MotorDynamicsLab/LDOVoronTrident/STLs/LDOSBCW2MountCover/LDOSBCW2MountCover.3mf

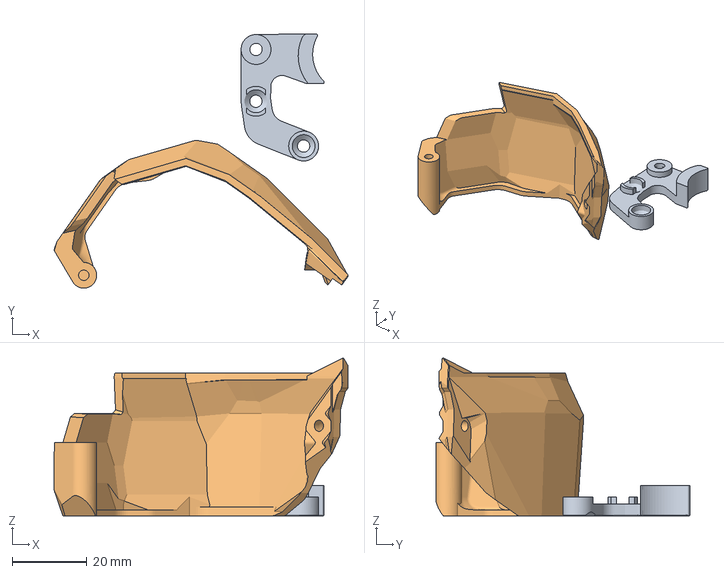
[picture p18: CAD file, 2022-08-31]
STLs/LDOSBCW2MountCover/LDOSBCW2MountCover.3mf
78.6 x 68.0 x 42.2 mm
