MotorDynamicsLab/LDOVoronTrident/STLs/LDOSBCW2MountCover/LDOSBCW2Cover.step

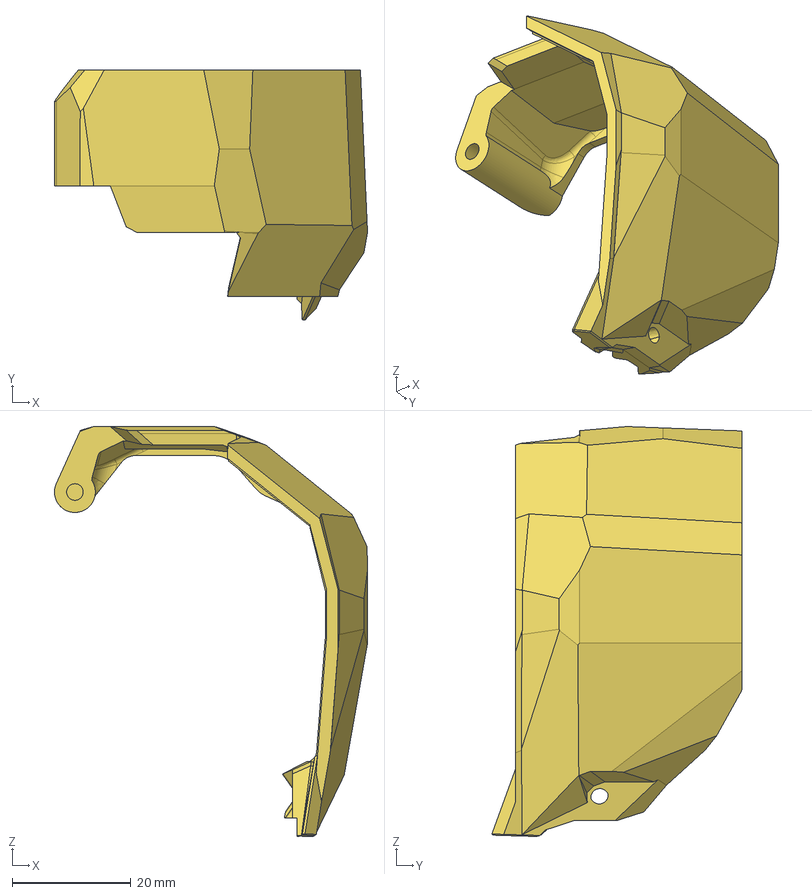
[picture p19: CAD file, 2022-08-31]
STLs/LDOSBCW2MountCover/LDOSBCW2Cover.step
52.8 x 42.2 x 69.1 mm
