MotorDynamicsLab/LDOVoronTrident/STLs/BTT Pi TFT4.3 Mount/mount_thick.stl

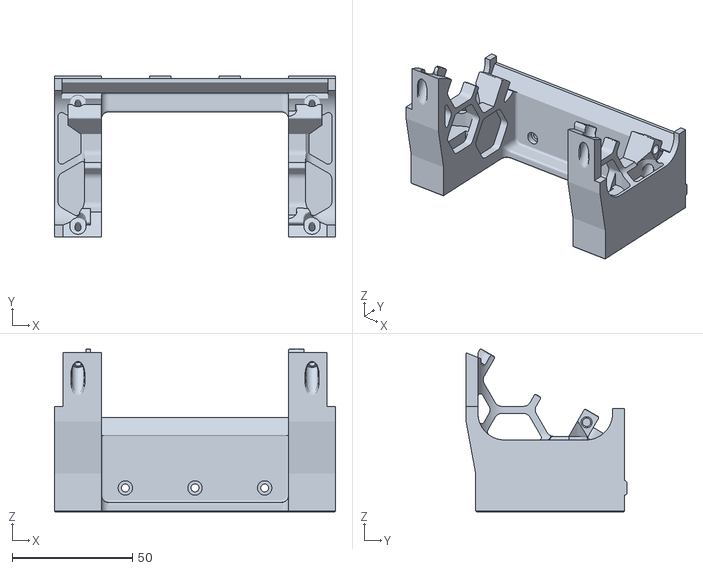
[picture p20: CAD file, 2024-01-23, an earlier design]
STLs/BTT Pi TFT4.3 Mount/mount_thick.stl
117.0 x 67.0 x 67.8
