MotorDynamicsLab/LDOVoronTrident/Images/WiringGuide/250/din_rails_close_up.jpg

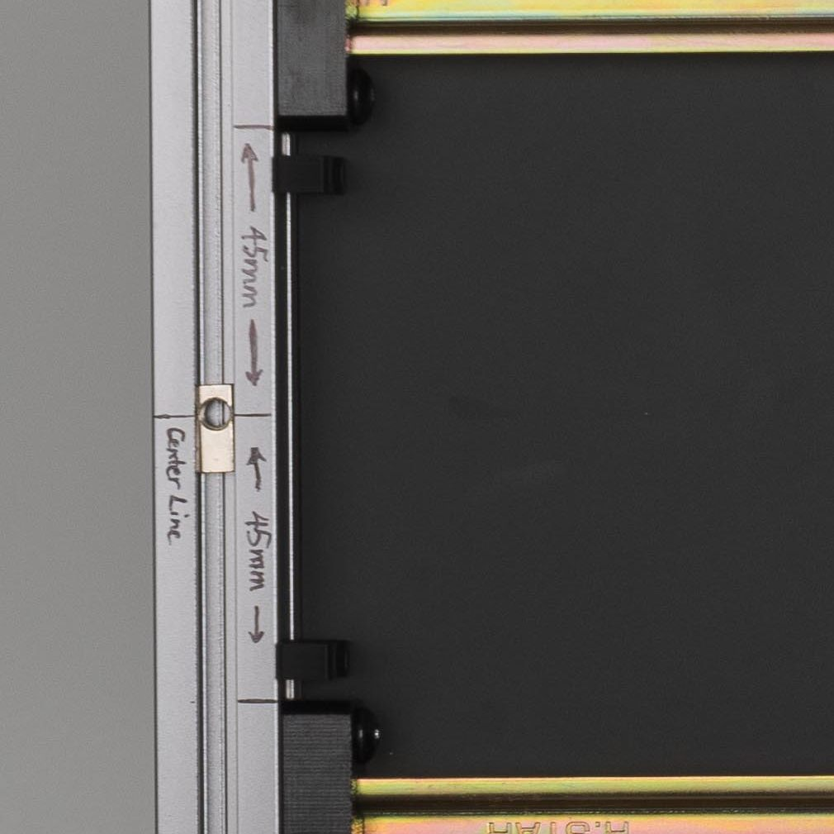
Images/WiringGuide/250/din_rails_close_up.jpg
