MotorDynamicsLab/LDOVoronTrident/Images/WiringGuide/250/fan_pcb_positioning.jpg

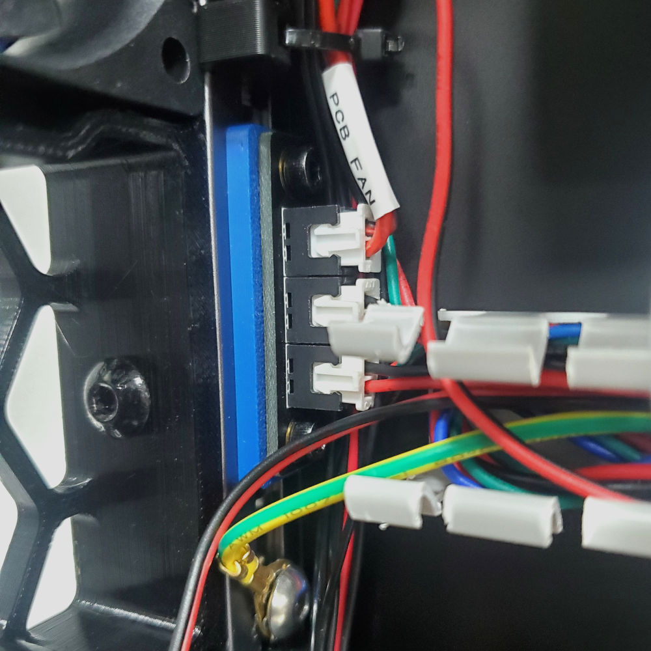
Images/WiringGuide/250/fan_pcb_positioning.jpg
