MotorDynamicsLab/LDOVoronTrident/Images/WiringGuide/250/S01_din_rails.jpg

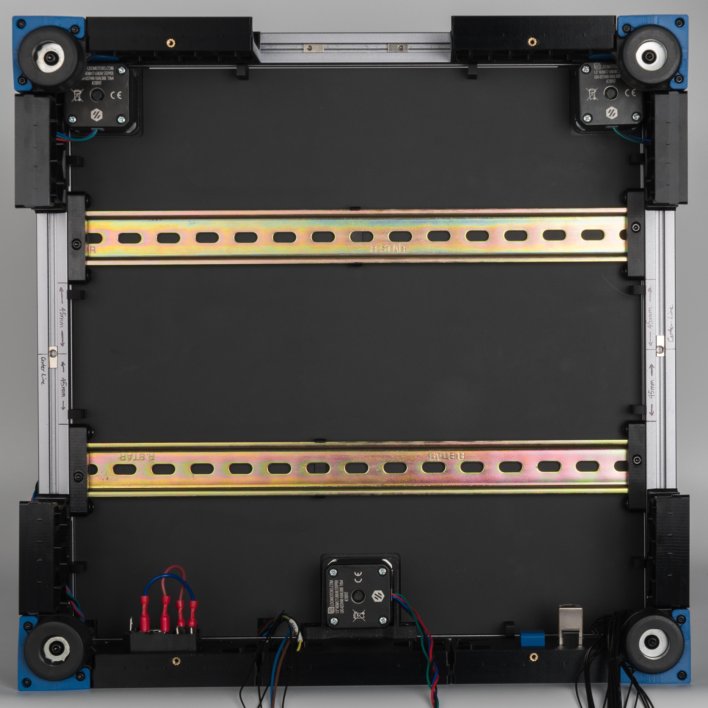
Images/WiringGuide/250/S01_din_rails.jpg
