MotorDynamicsLab/LDOVoronTrident/Images/WiringGuide/250/S02_general_placement.jpg

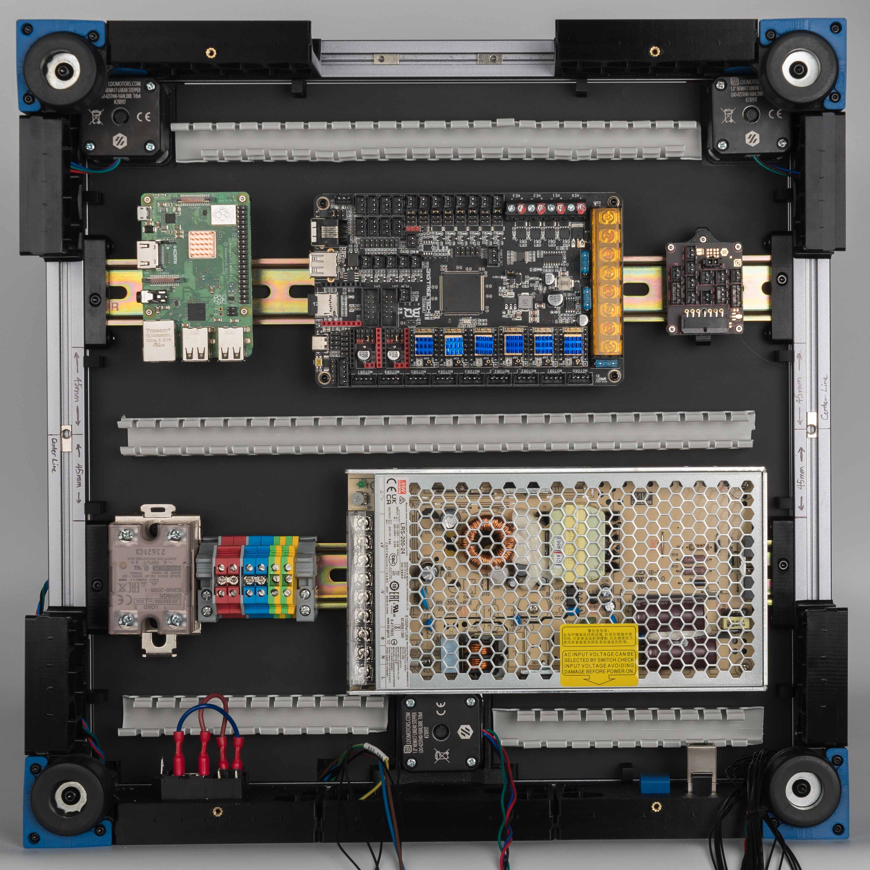
Images/WiringGuide/250/S02_general_placement.jpg
