MotorDynamicsLab/LDOVoronTrident/Images/WiringGuide/250/s03_mapping.png

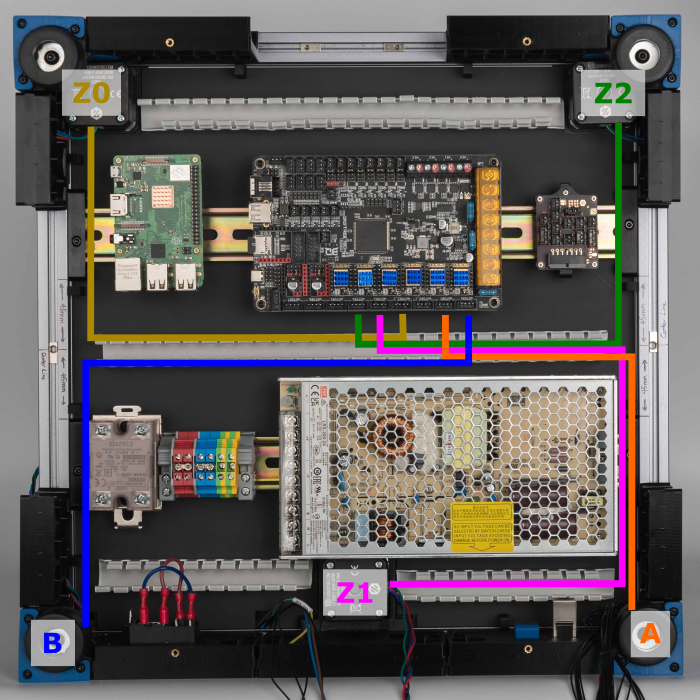
Images/WiringGuide/250/s03_mapping.png
