MotorDynamicsLab/LDOVoronTrident/Images/WiringGuide/250/S03_steppers.jpg

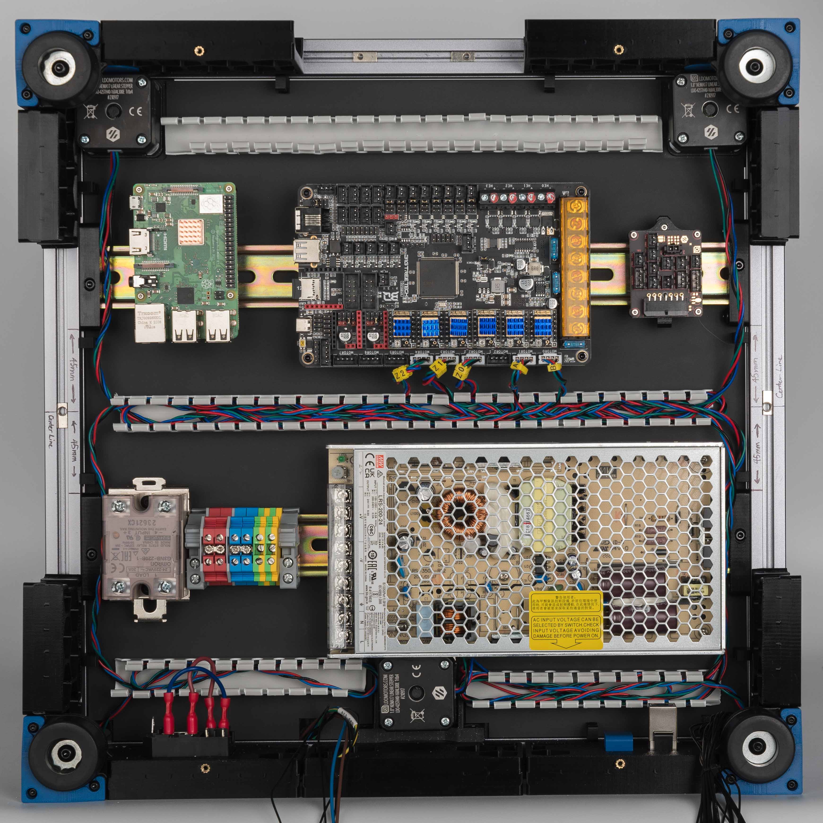
Images/WiringGuide/250/S03_steppers.jpg
