MotorDynamicsLab/LDOVoronTrident/Images/WiringGuide/250/s04_inlet_psu.jpg

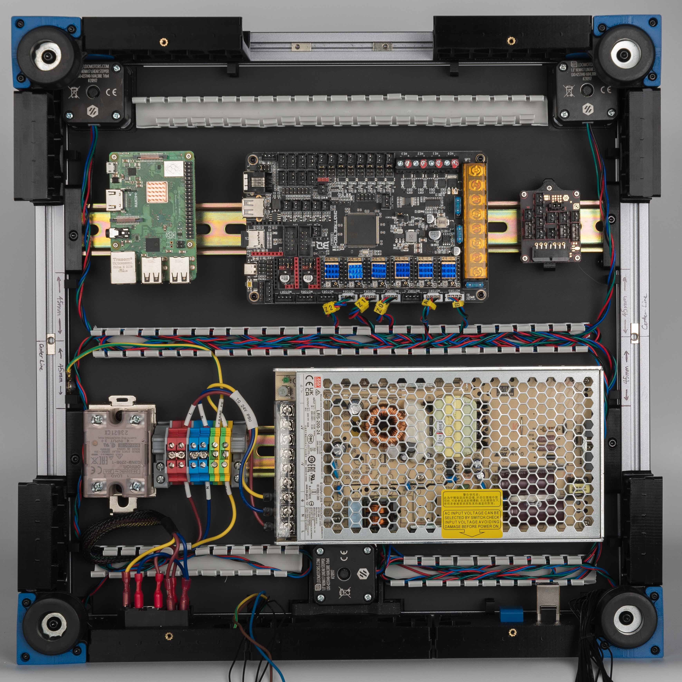
Images/WiringGuide/250/s04_inlet_psu.jpg
