MotorDynamicsLab/LDOVoronTrident/Images/WiringGuide/250/s04_mapping.png

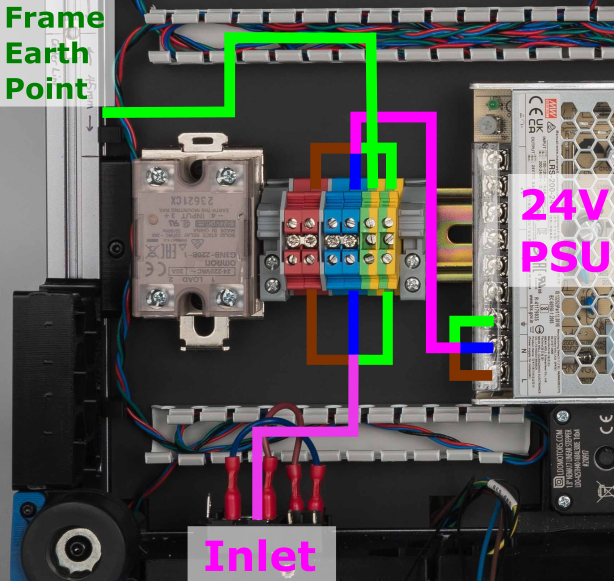
Images/WiringGuide/250/s04_mapping.png
