MotorDynamicsLab/LDOVoronTrident/Images/WiringGuide/250/s06_bed_controller.jpg

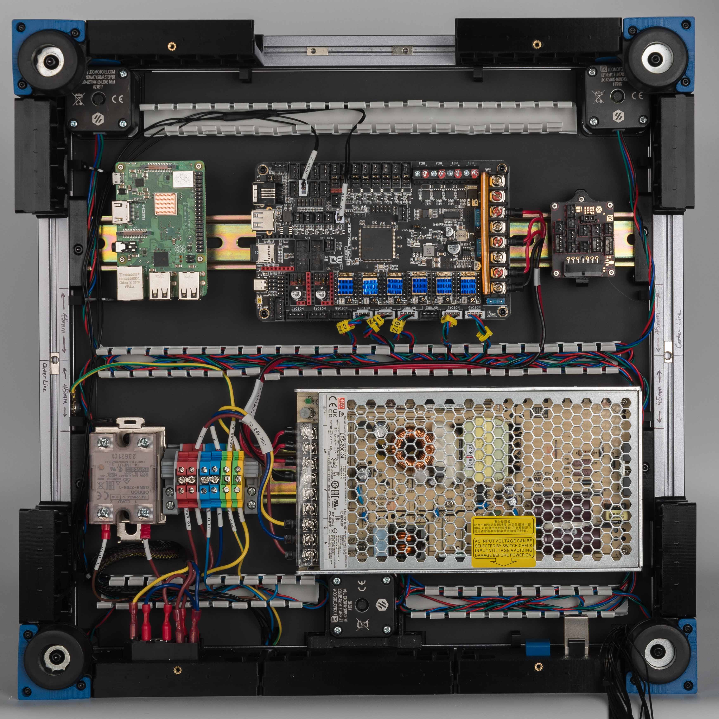
Images/WiringGuide/250/s06_bed_controller.jpg
