MotorDynamicsLab/LDOVoronTrident/Images/WiringGuide/250/s06_mapping.png

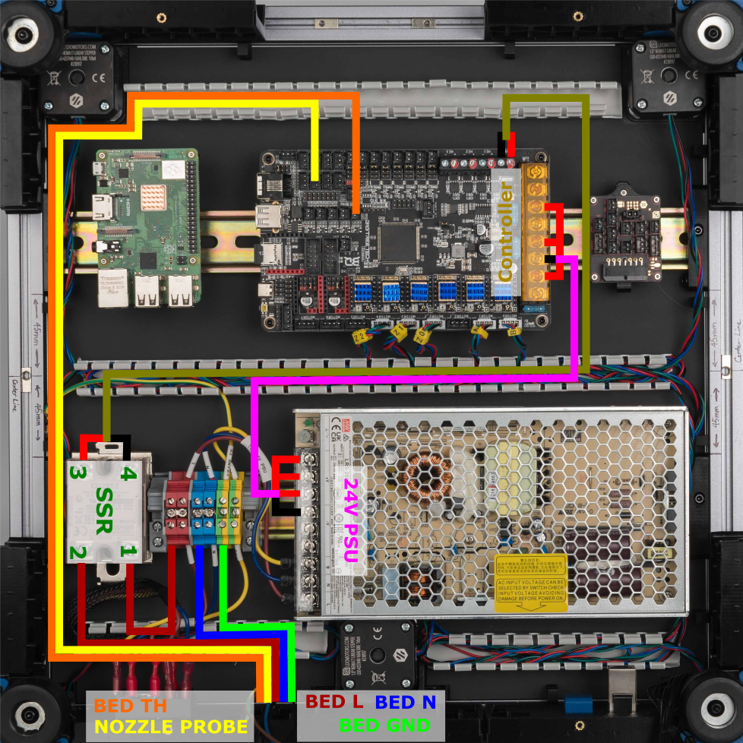
Images/WiringGuide/250/s06_mapping.png
