MotorDynamicsLab/LDOVoronTrident/Images/WiringGuide/250/s07_mapping.png

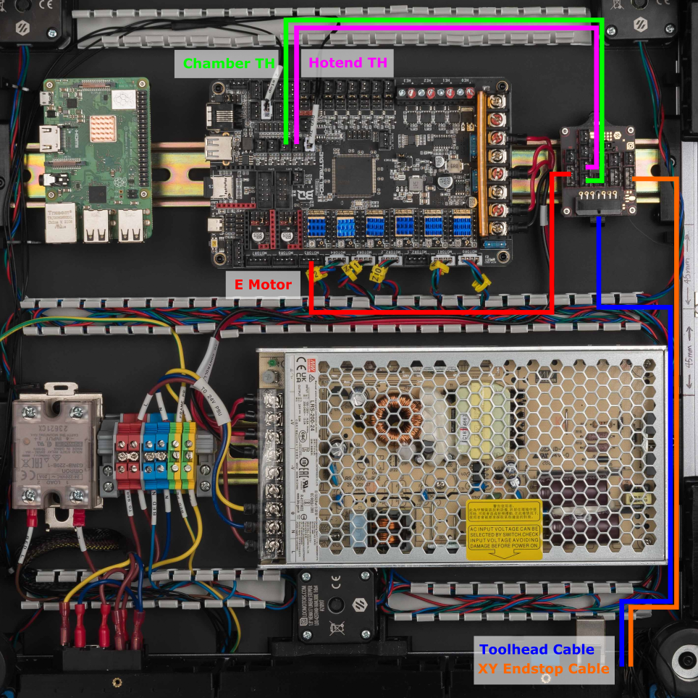
Images/WiringGuide/250/s07_mapping.png
