MotorDynamicsLab/LDOVoronTrident/Images/WiringGuide/250/s07_toolhead_th_motor.jpg

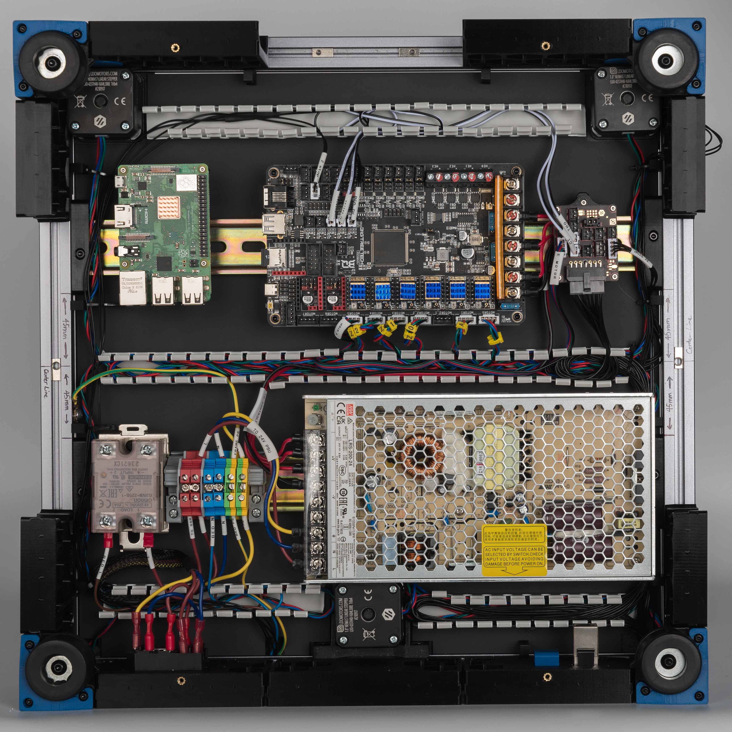
Images/WiringGuide/250/s07_toolhead_th_motor.jpg
