MotorDynamicsLab/LDOVoronTrident/Images/WiringGuide/250/s08_mapping.png

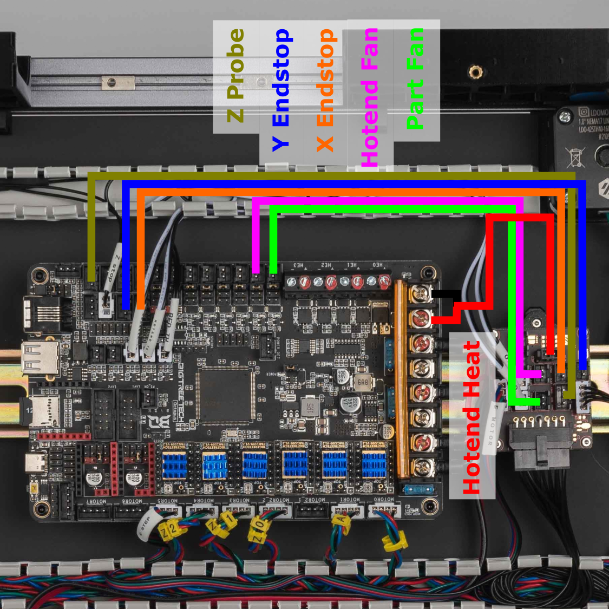
Images/WiringGuide/250/s08_mapping.png
