MotorDynamicsLab/LDOVoronTrident/Images/WiringGuide/250/s09_mapping.png

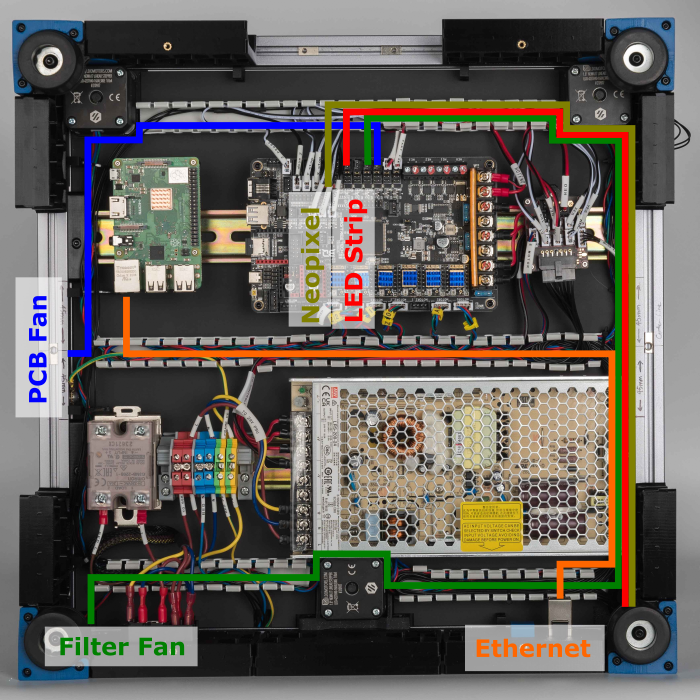
Images/WiringGuide/250/s09_mapping.png
