MotorDynamicsLab/LDOVoronTrident/Images/WiringGuide/250/s09_misc.jpg

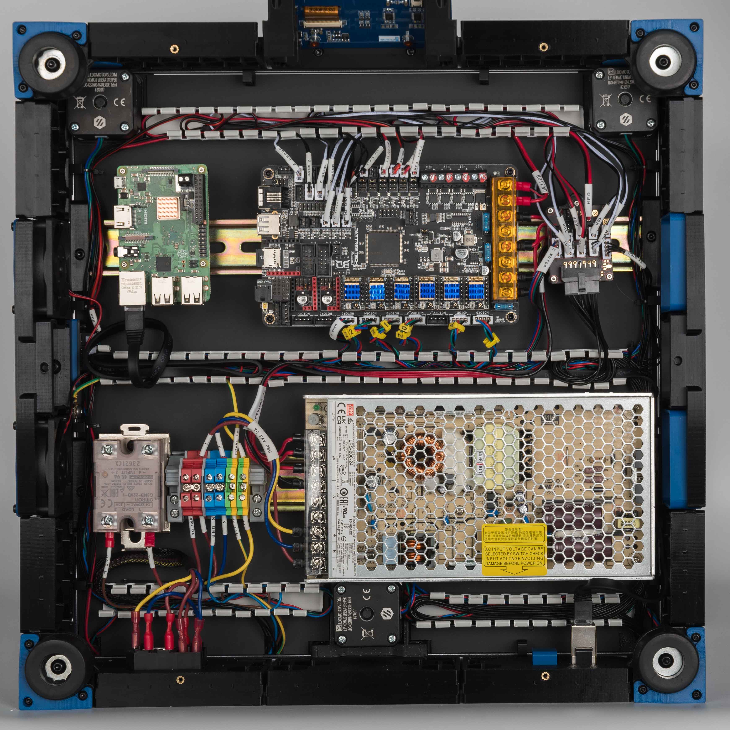
Images/WiringGuide/250/s09_misc.jpg
