MotorDynamicsLab/LDOVoronTrident/Images/WiringGuide/250/s10_mapping.png

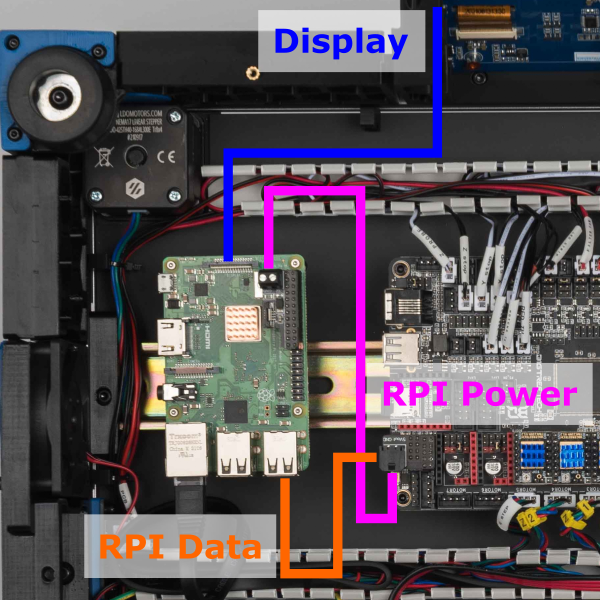
Images/WiringGuide/250/s10_mapping.png
