MotorDynamicsLab/LDOVoronTrident/Images/WiringGuide/250/s10_rpi.jpg

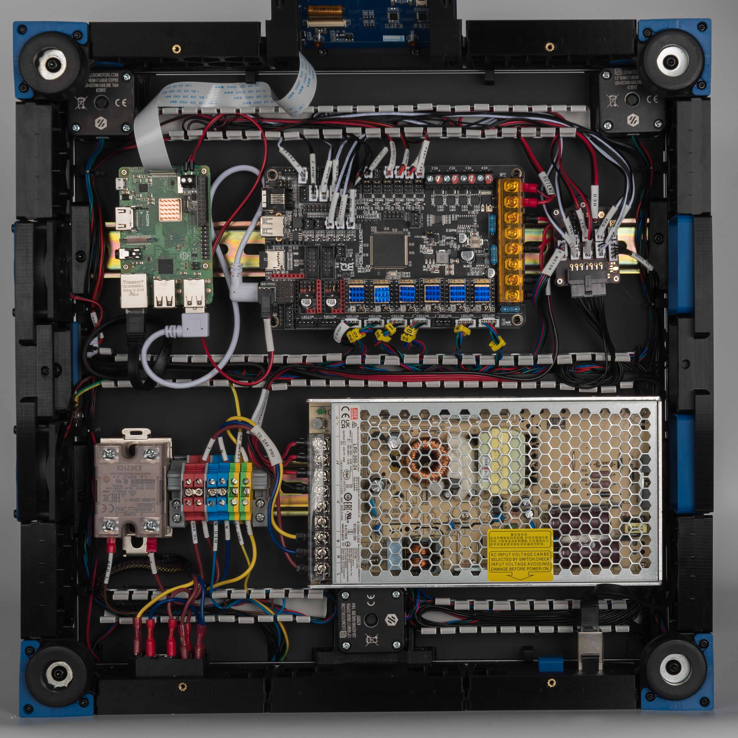
Images/WiringGuide/250/s10_rpi.jpg
