MotorDynamicsLab/LDOVoronTrident/Images/WiringGuide/250/s11_duct_cover.jpg

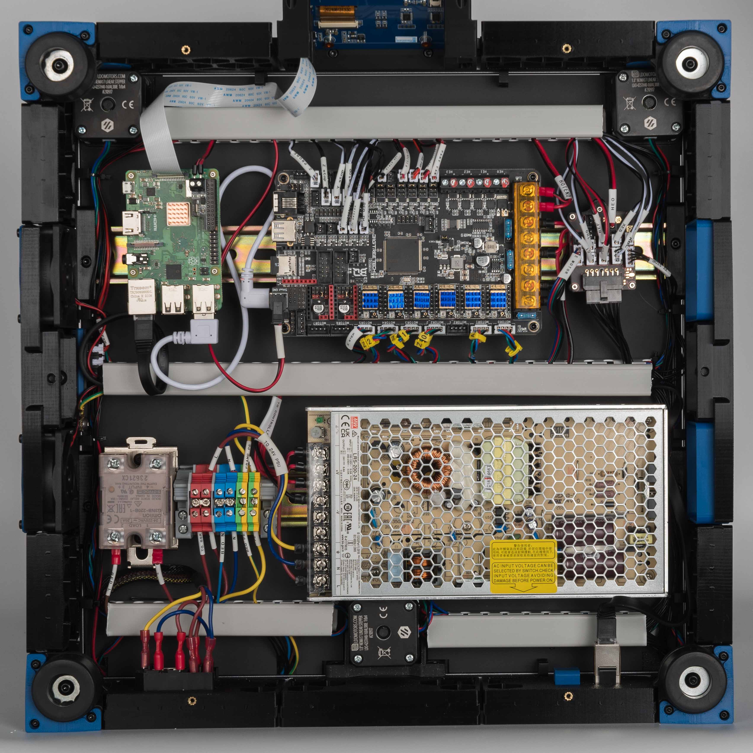
Images/WiringGuide/250/s11_duct_cover.jpg
