MotorDynamicsLab/LDOVoronTrident/Images/WiringGuide/build_plate_unwired.jpg

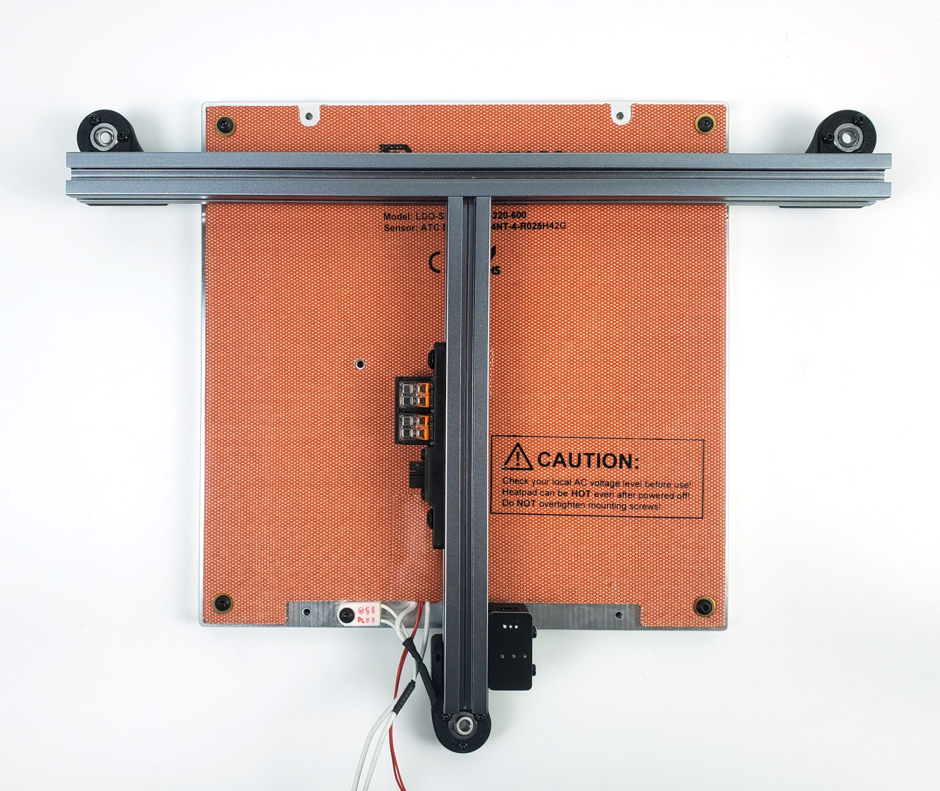
Images/WiringGuide/build_plate_unwired.jpg
