MotorDynamicsLab/LDOVoronTrident/Images/WiringGuide/build_plate_wired.jpg

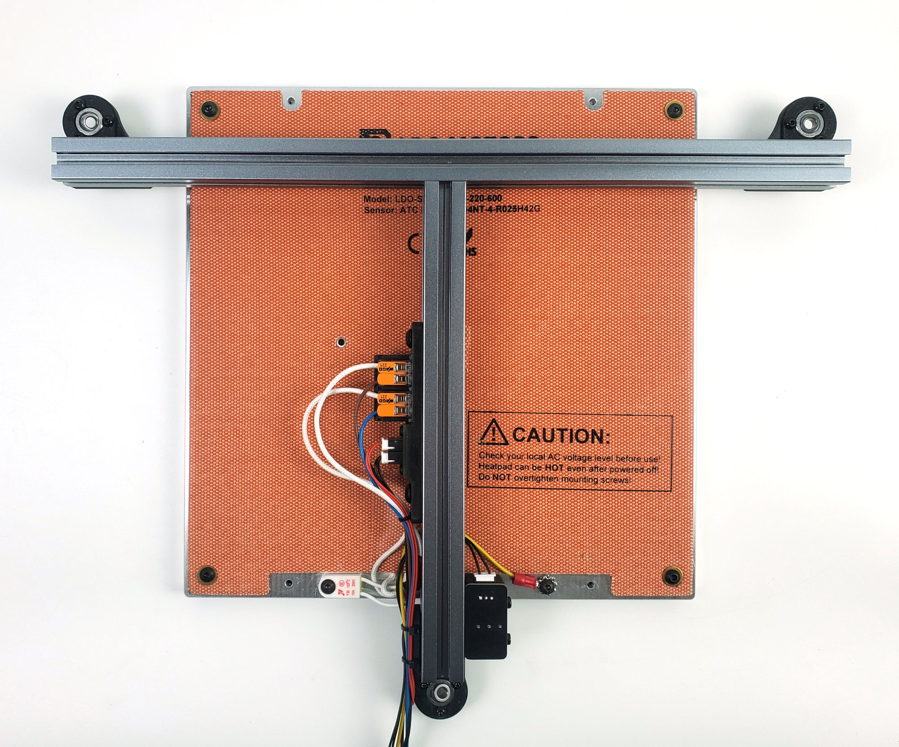
Images/WiringGuide/build_plate_wired.jpg
