MotorDynamicsLab/LDOVoronTrident/Images/WiringGuide/display_connection_a.jpg

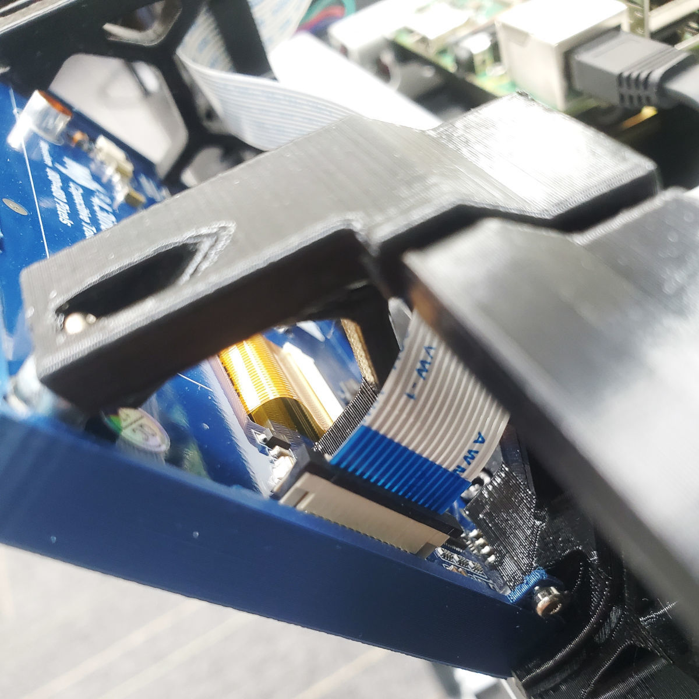
Images/WiringGuide/display_connection_a.jpg
