MotorDynamicsLab/LDOVoronTrident/Images/WiringGuide/display_connection_b.jpg

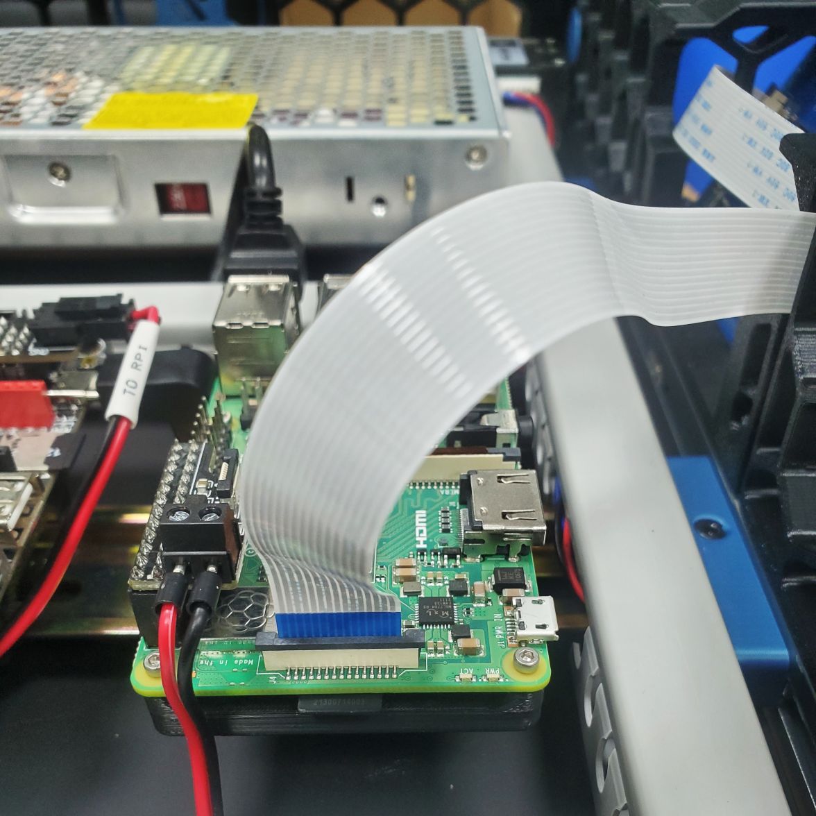
Images/WiringGuide/display_connection_b.jpg
