MotorDynamicsLab/LDOVoronTrident/Images/WiringGuide/frame_grounding.jpg

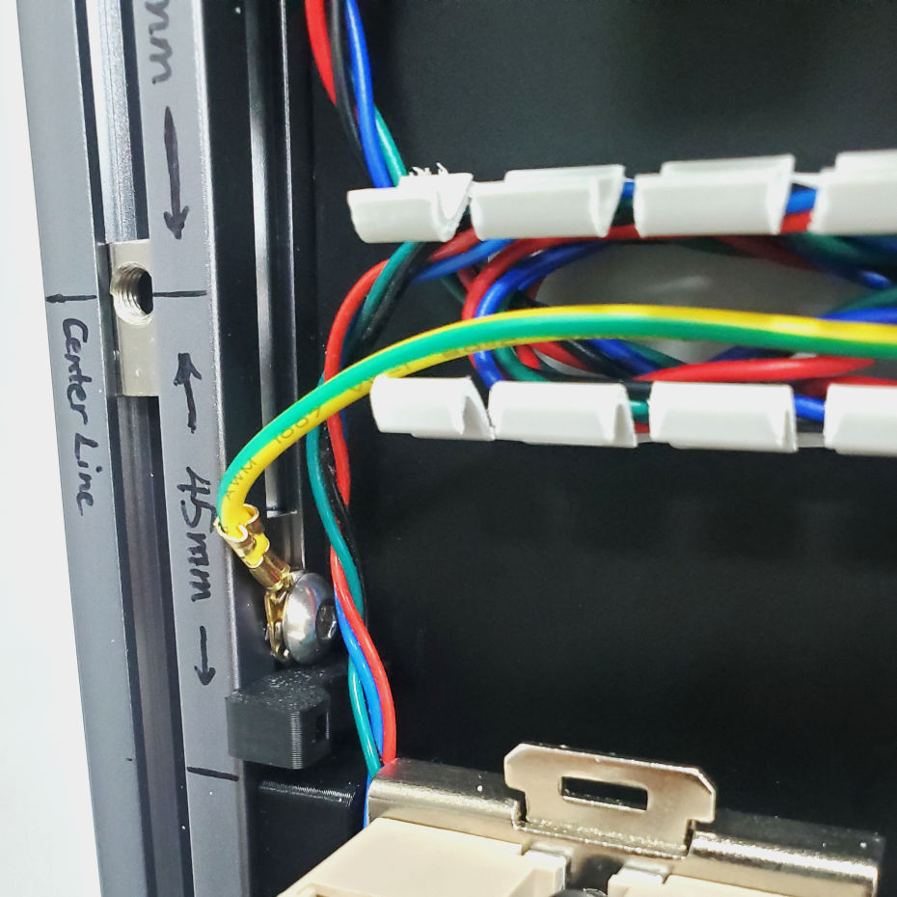
Images/WiringGuide/frame_grounding.jpg
