MotorDynamicsLab/LDOVoronTrident/Images/WiringGuide/led_pcb_positioning.jpg

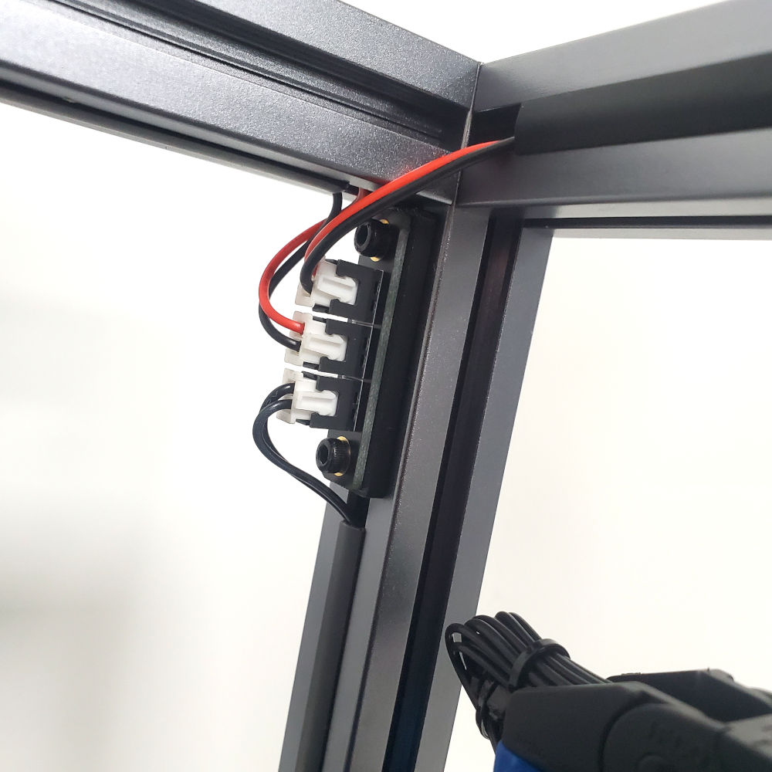
Images/WiringGuide/led_pcb_positioning.jpg
