MotorDynamicsLab/LDOVoronTrident/Images/WiringGuide/led_route.png

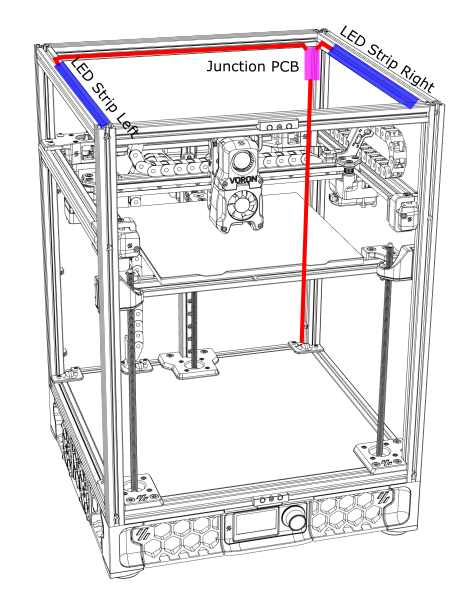
Images/WiringGuide/led_route.png
