MotorDynamicsLab/LDOVoronTrident/Images/WiringGuide/Octopus_Populated.jpg

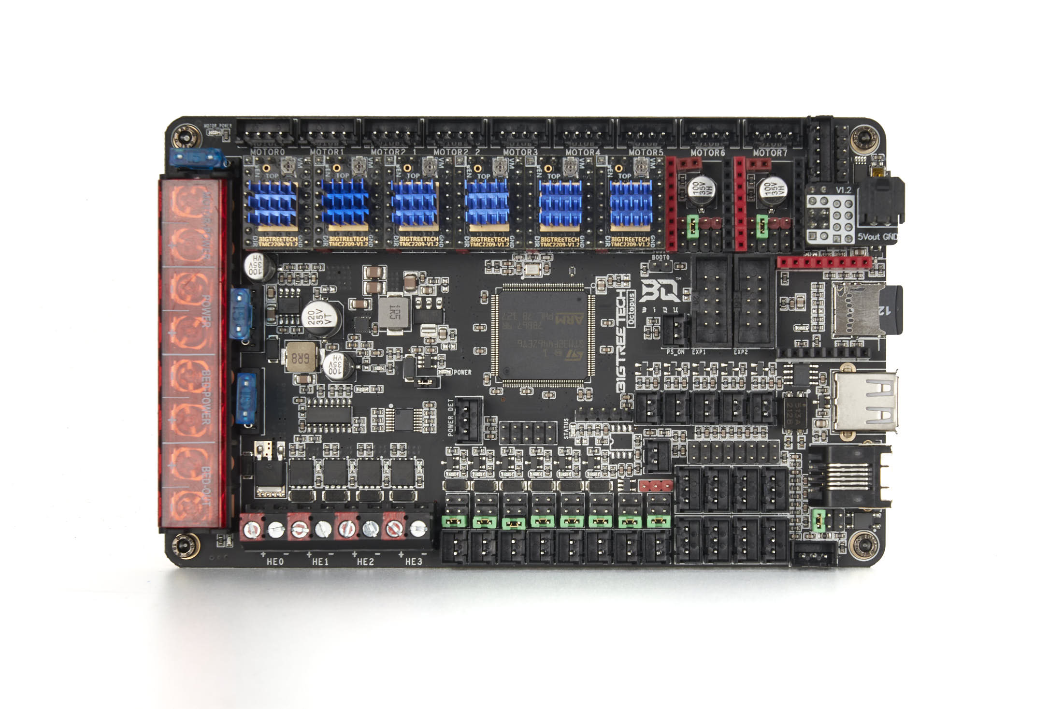
Images/WiringGuide/Octopus_Populated.jpg
