MotorDynamicsLab/LDOVoronTrident/Images/WiringGuide/rail_close_up.png

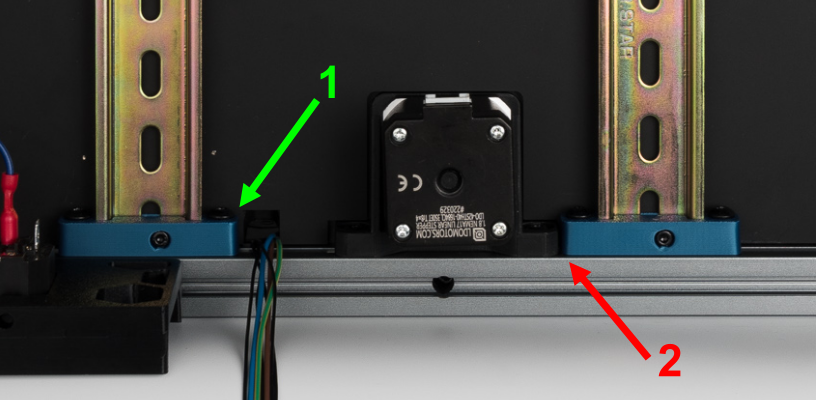
Images/WiringGuide/rail_close_up.png
