MotorDynamicsLab/LDOVoronTrident/Images/WiringGuide/raspi_power_connection.jpg

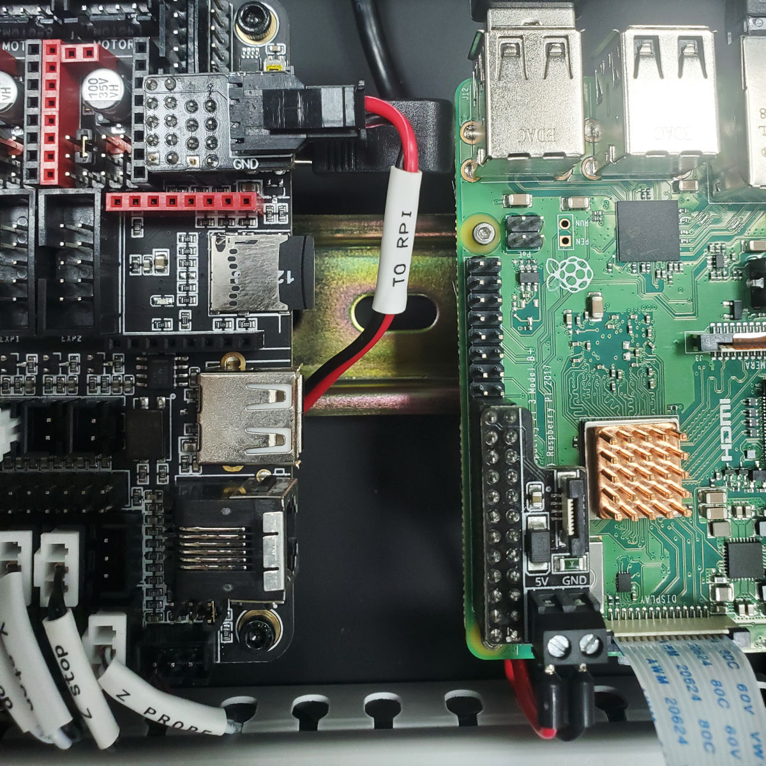
Images/WiringGuide/raspi_power_connection.jpg
