MotorDynamicsLab/LDOVoronTrident/Images/WiringGuide/RevD/00_Din Rail.jpg

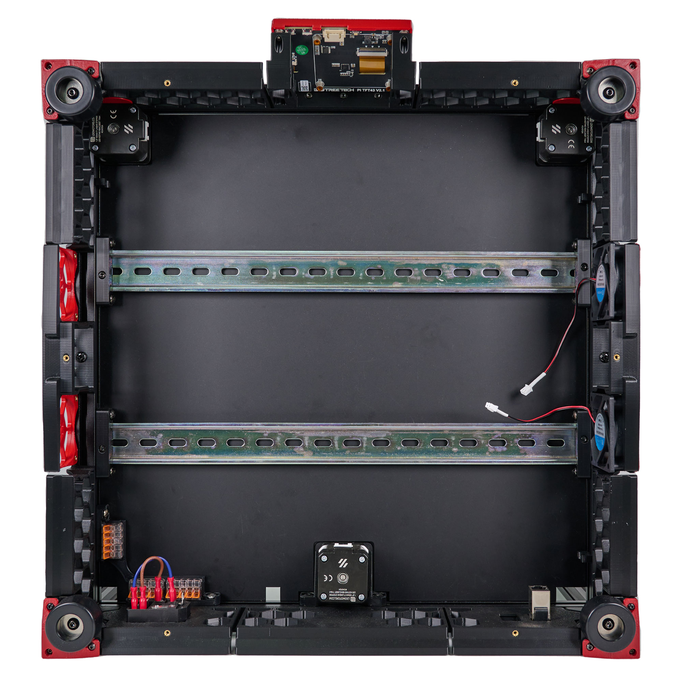
Images/WiringGuide/RevD/00_Din Rail.jpg
