MotorDynamicsLab/LDOVoronTrident/Images/WiringGuide/RevD/00_Gneral Placement.jpg

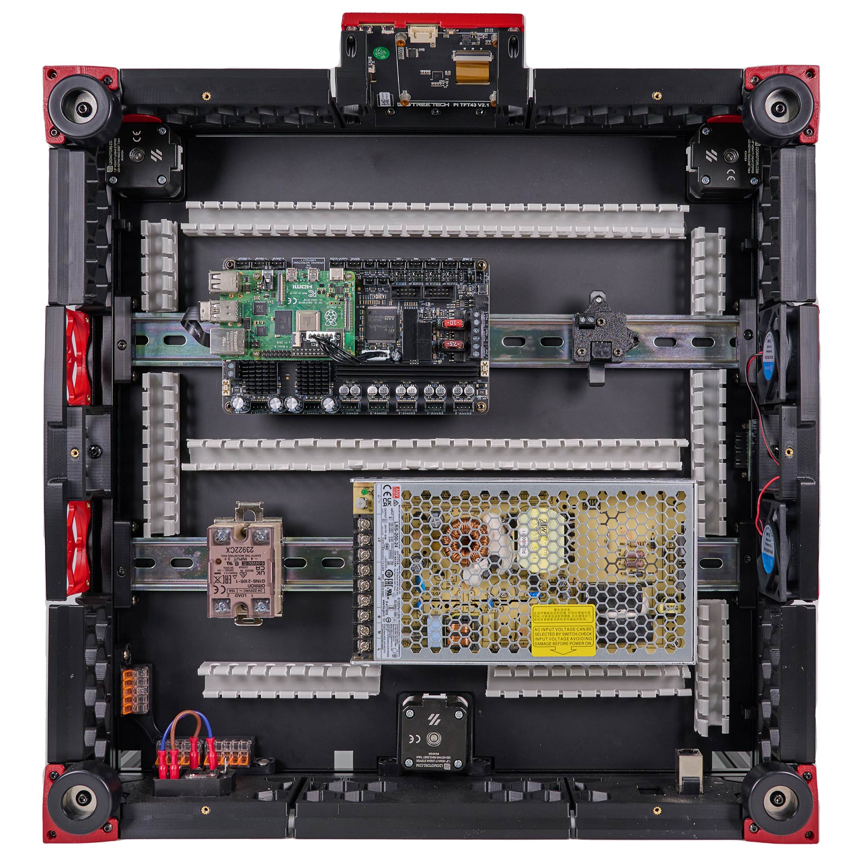
Images/WiringGuide/RevD/00_Gneral Placement.jpg
