MotorDynamicsLab/LDOVoronTrident/Images/WiringGuide/RevD/02_inlet.jpg

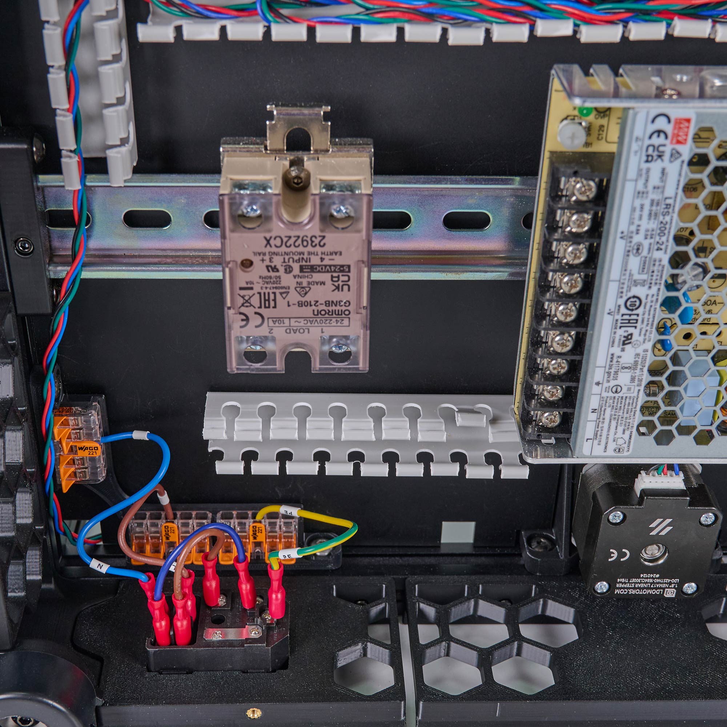
Images/WiringGuide/RevD/02_inlet.jpg
