MotorDynamicsLab/LDOVoronTrident/Images/WiringGuide/RevD/02_mapping.jpg

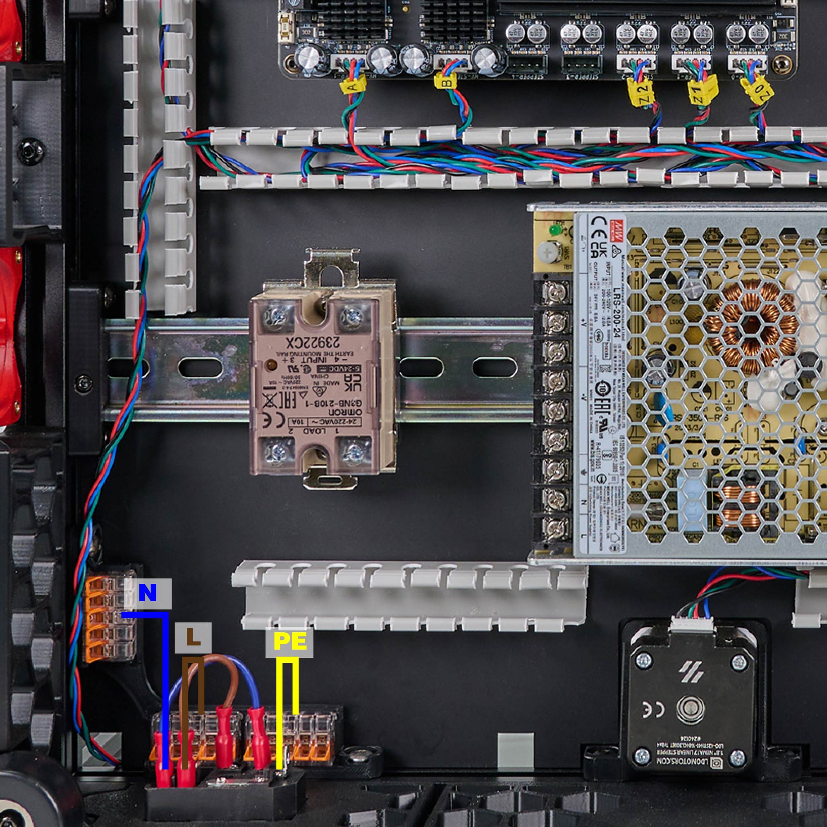
Images/WiringGuide/RevD/02_mapping.jpg
