MotorDynamicsLab/LDOVoronTrident/Images/WiringGuide/RevD/03Wgo_PSU.jpg

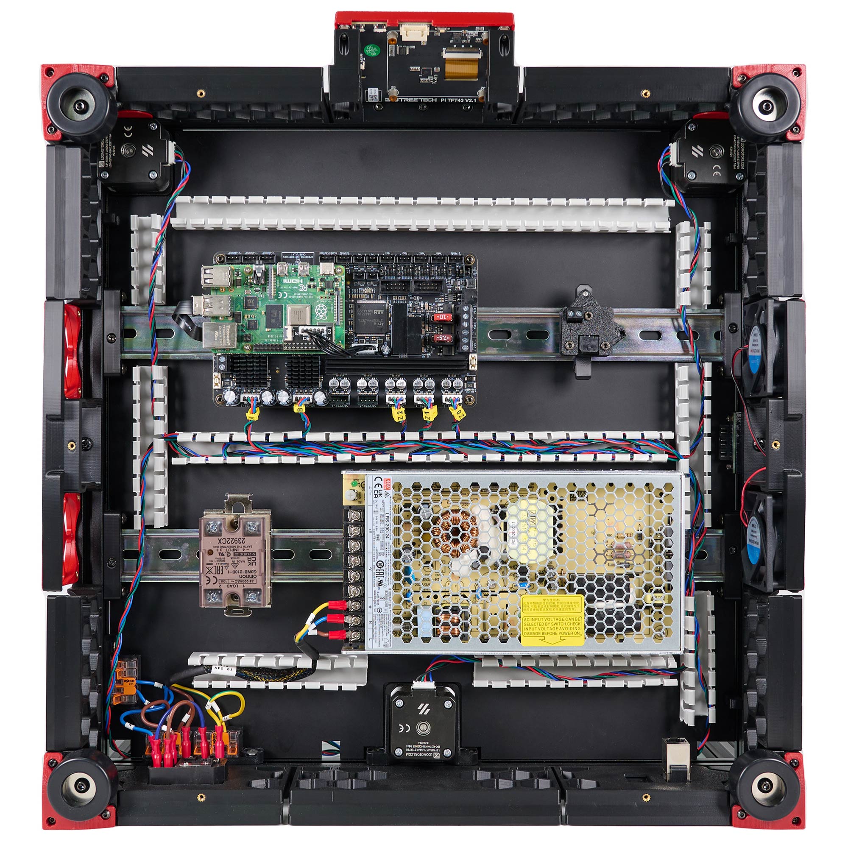
Images/WiringGuide/RevD/03Wgo_PSU.jpg
