MotorDynamicsLab/LDOVoronTrident/Images/WiringGuide/RevD/04_PSU_MB.jpg

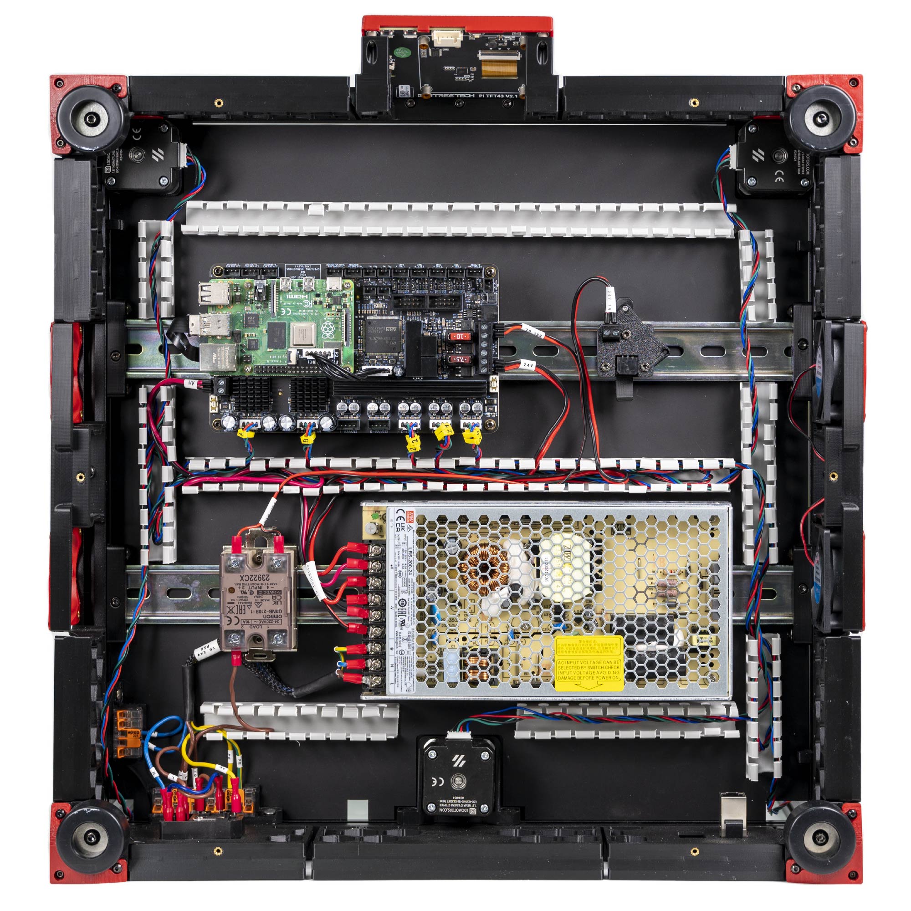
Images/WiringGuide/RevD/04_PSU_MB.jpg
