MotorDynamicsLab/LDOVoronTrident/Images/WiringGuide/RevD/06_Endstop.jpg

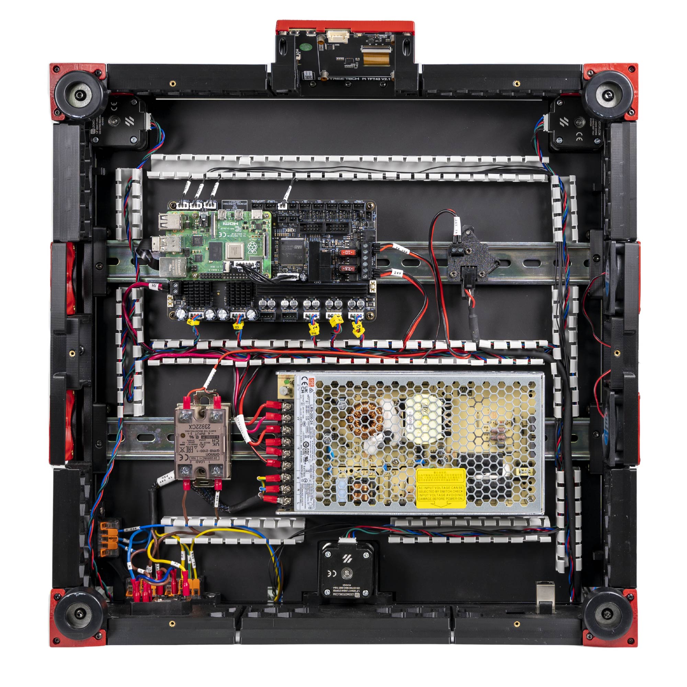
Images/WiringGuide/RevD/06_Endstop.jpg
