MotorDynamicsLab/LDOVoronTrident/Images/WiringGuide/RevD/06_mapping.jpg

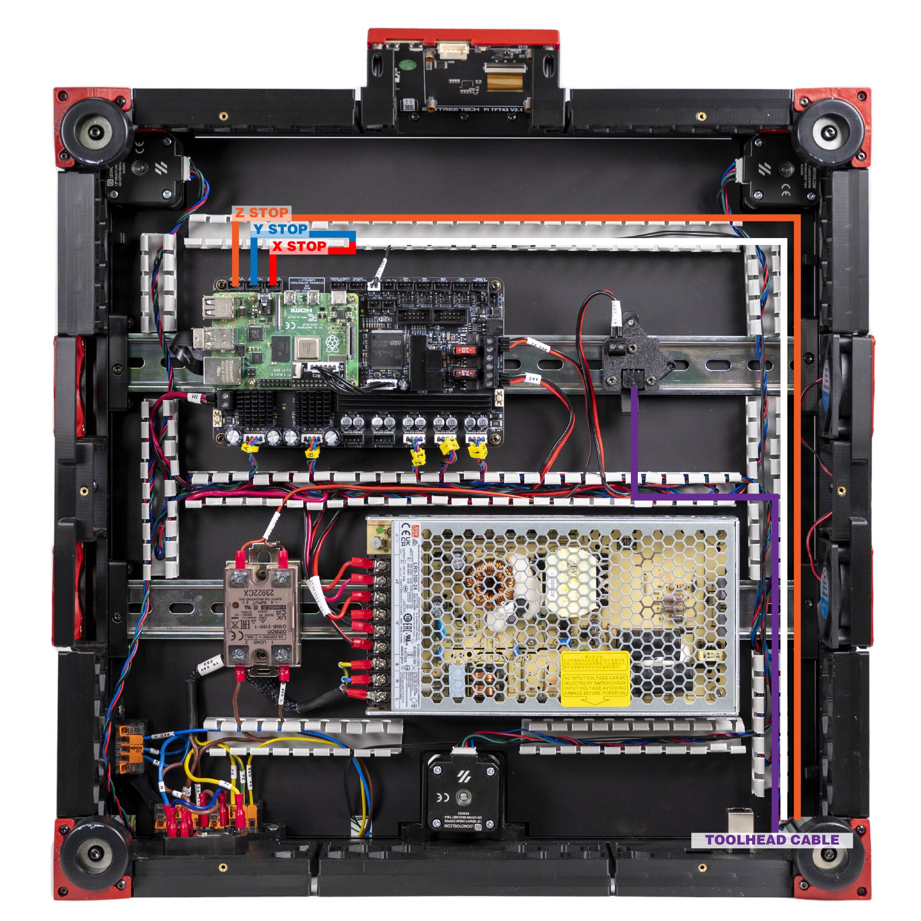
Images/WiringGuide/RevD/06_mapping.jpg
