MotorDynamicsLab/LDOVoronTrident/Images/WiringGuide/RevD/08_Touch Display.jpg

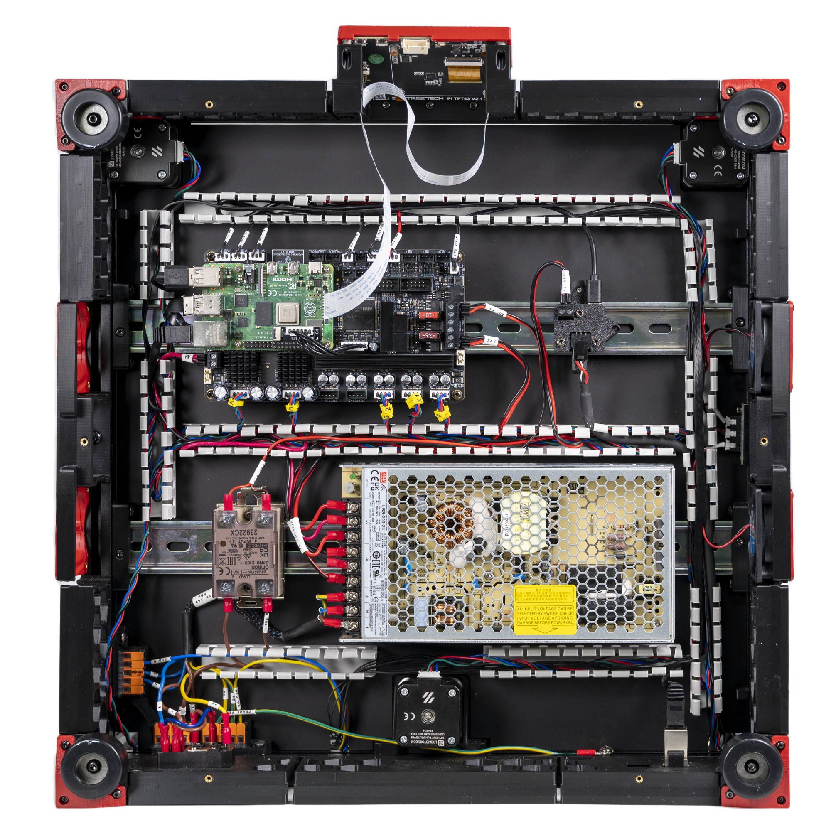
Images/WiringGuide/RevD/08_Touch Display.jpg
