MotorDynamicsLab/LDOVoronTrident/Images/WiringGuide/RevD/09_Final.jpg

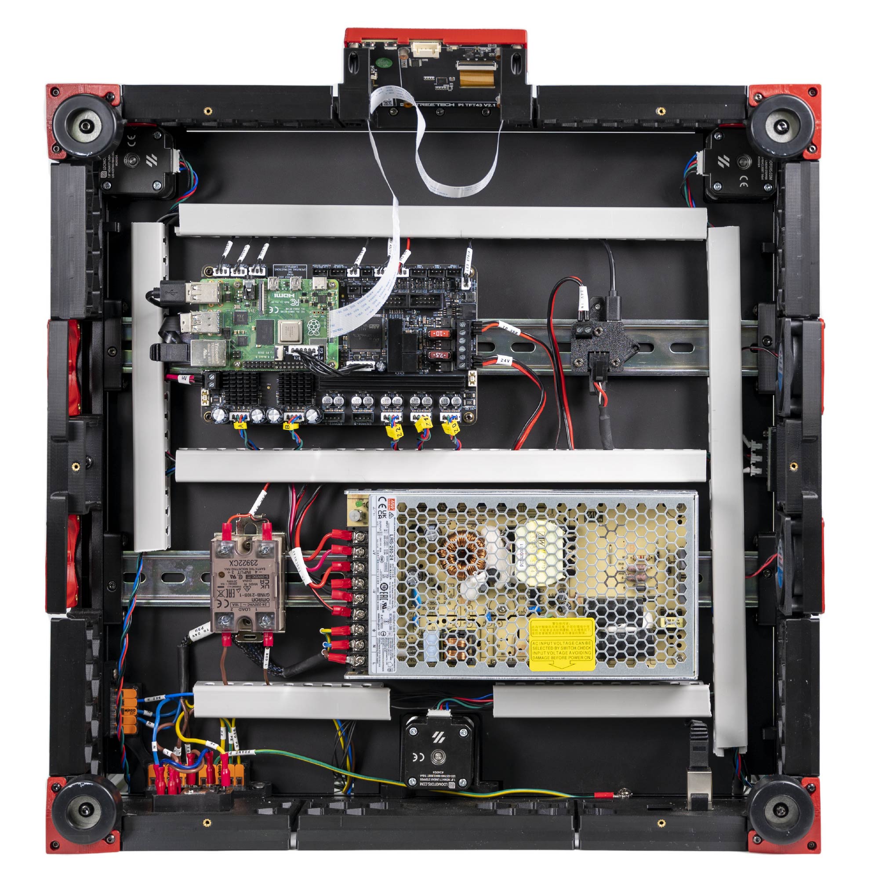
Images/WiringGuide/RevD/09_Final.jpg
