MotorDynamicsLab/LDOVoronTrident/Images/WiringGuide/S01_DIN_Rails.jpg

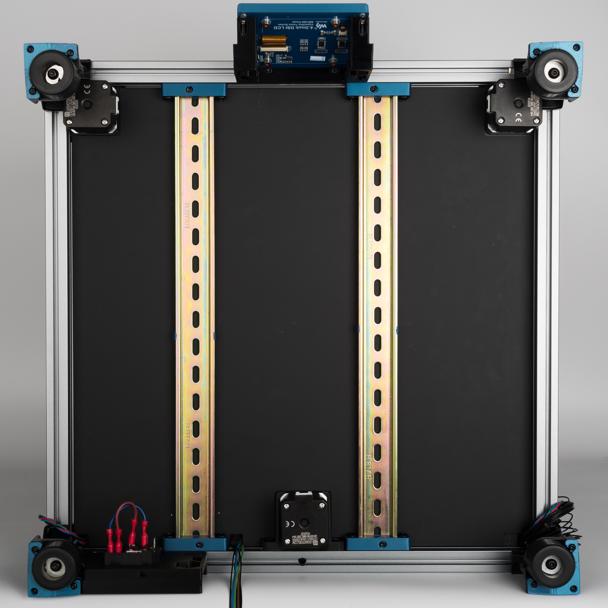
Images/WiringGuide/S01_DIN_Rails.jpg
