MotorDynamicsLab/LDOVoronTrident/Images/WiringGuide/s03_mapping.png

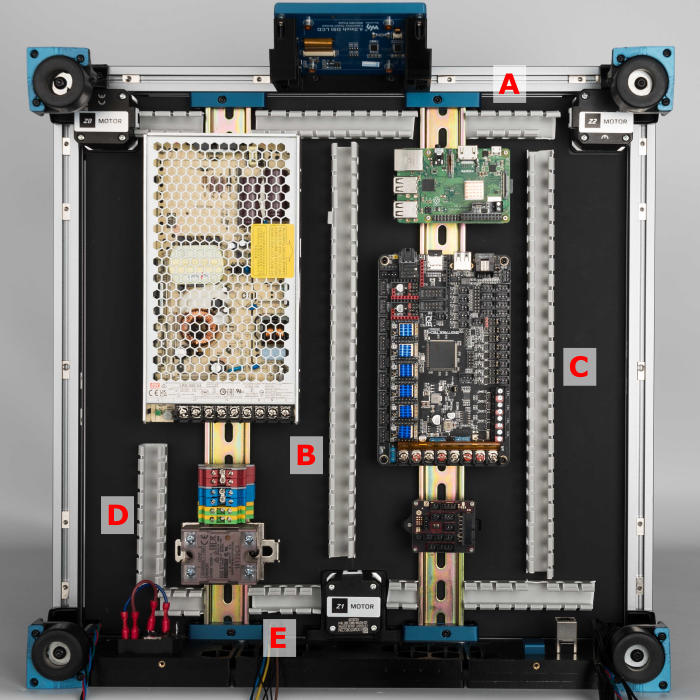
Images/WiringGuide/s03_mapping.png
