MotorDynamicsLab/LDOVoronTrident/Images/WiringGuide/s03_wire_ducts.jpg

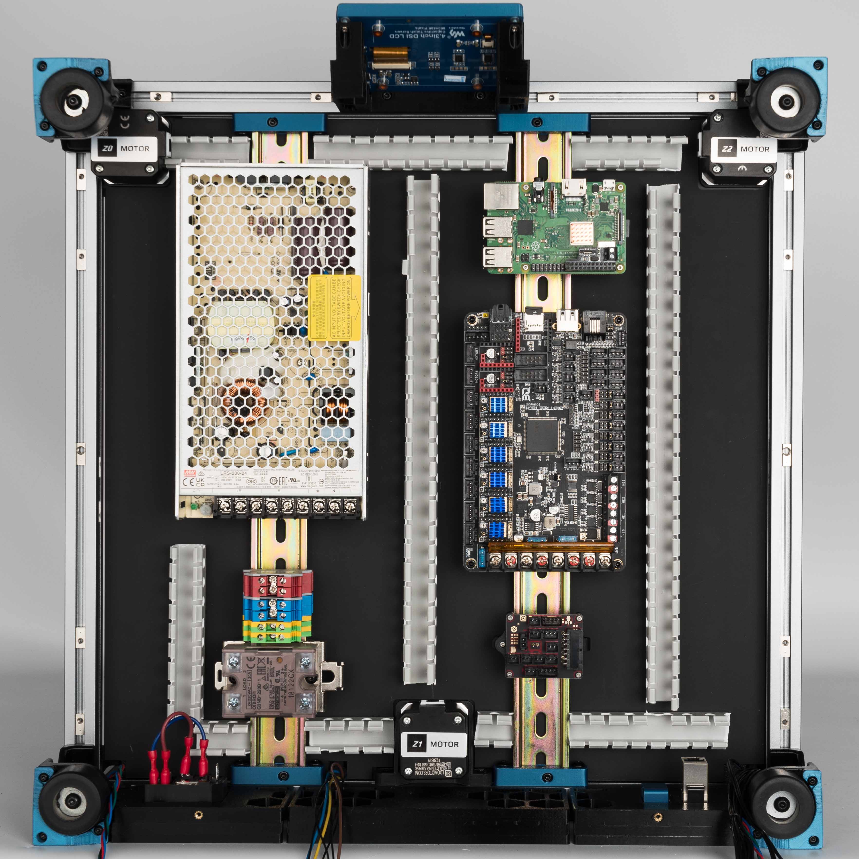
Images/WiringGuide/s03_wire_ducts.jpg
