MotorDynamicsLab/LDOVoronTrident/Images/WiringGuide/s04_mapping.png

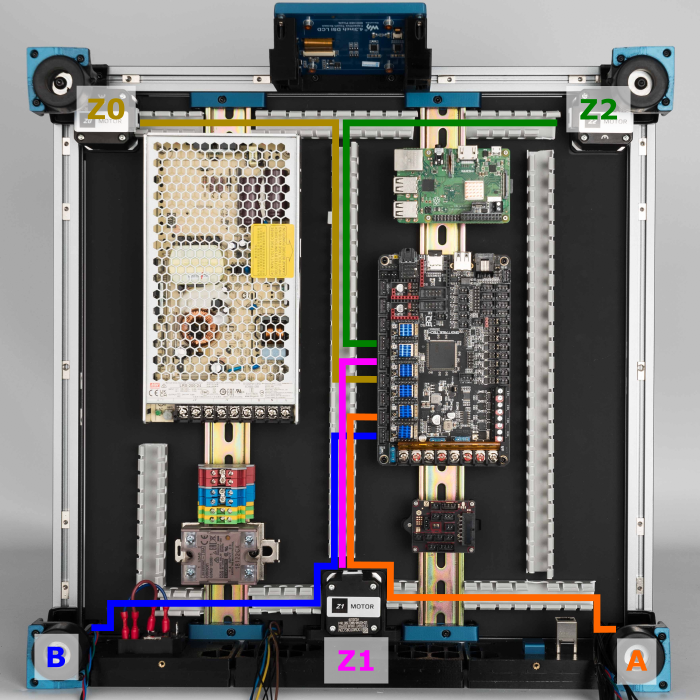
Images/WiringGuide/s04_mapping.png
