MotorDynamicsLab/LDOVoronTrident/Images/WiringGuide/s05_mapping.png

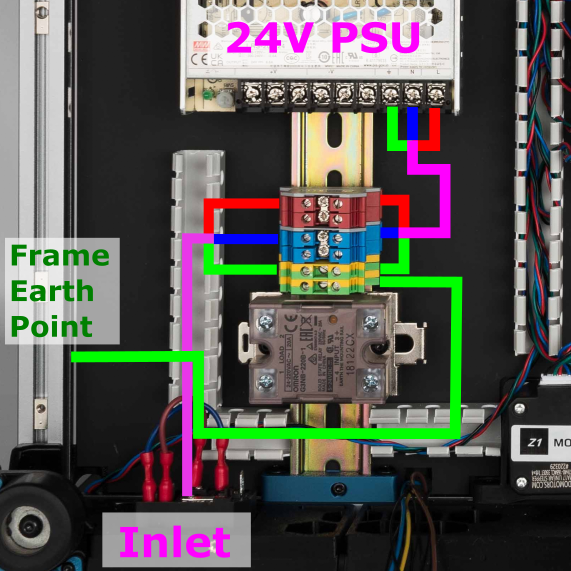
Images/WiringGuide/s05_mapping.png
