MotorDynamicsLab/LDOVoronTrident/Images/WiringGuide/s07_mapping.png

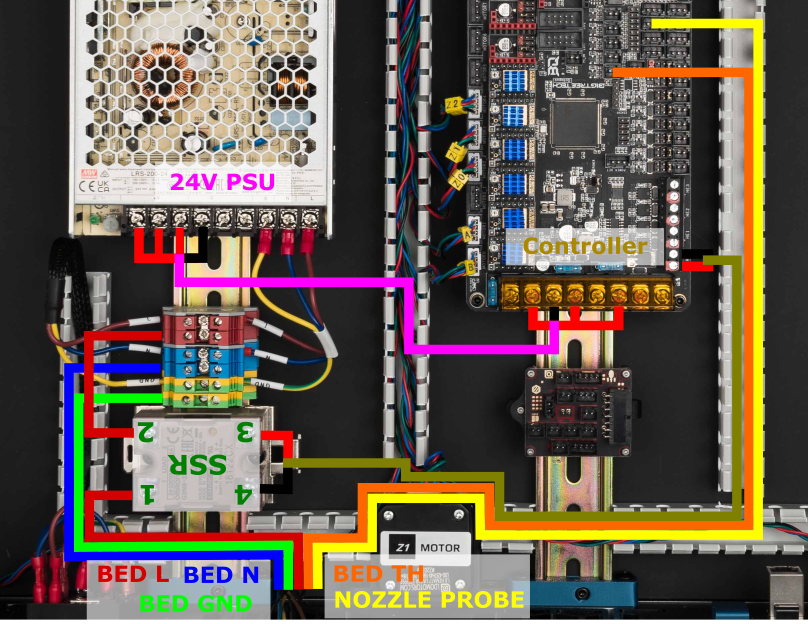
Images/WiringGuide/s07_mapping.png
