MotorDynamicsLab/LDOVoronTrident/Images/WiringGuide/s10_mapping.png

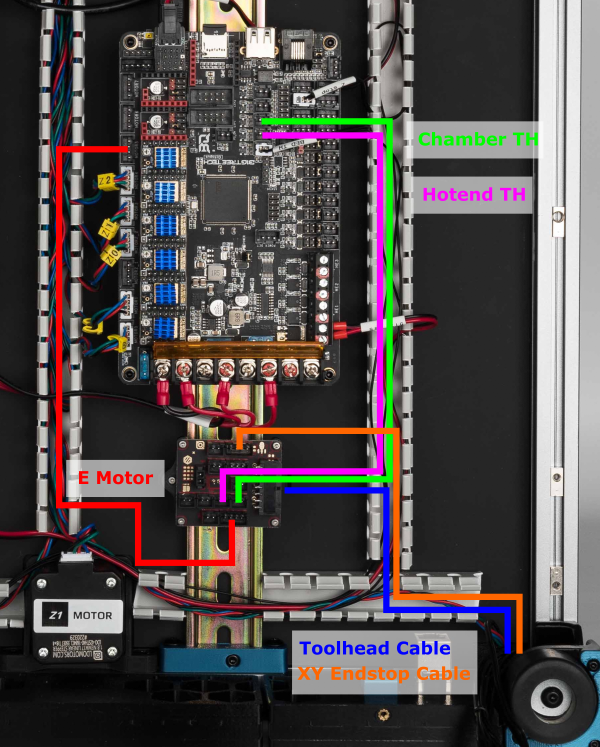
Images/WiringGuide/s10_mapping.png
