MotorDynamicsLab/LDOVoronTrident/Images/WiringGuide/s12_mapping.png

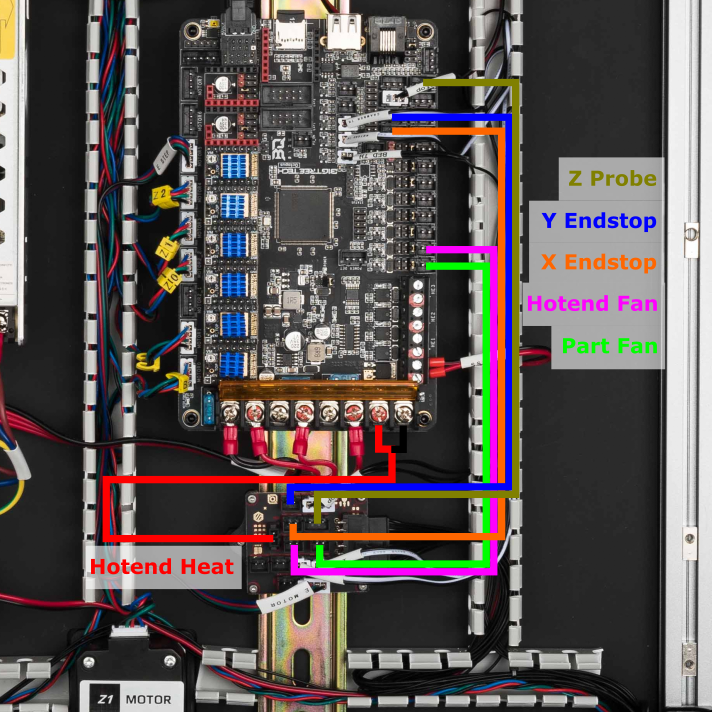
Images/WiringGuide/s12_mapping.png
