MotorDynamicsLab/LDOVoronTrident/Images/WiringGuide/s14_mapping.png

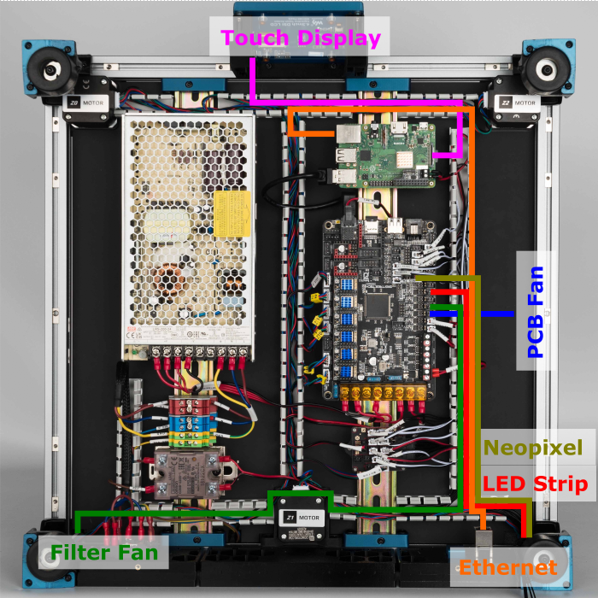
Images/WiringGuide/s14_mapping.png
