MotorDynamicsLab/LDOVoronTrident/Images/WiringGuide/s15_duct_cover.jpg

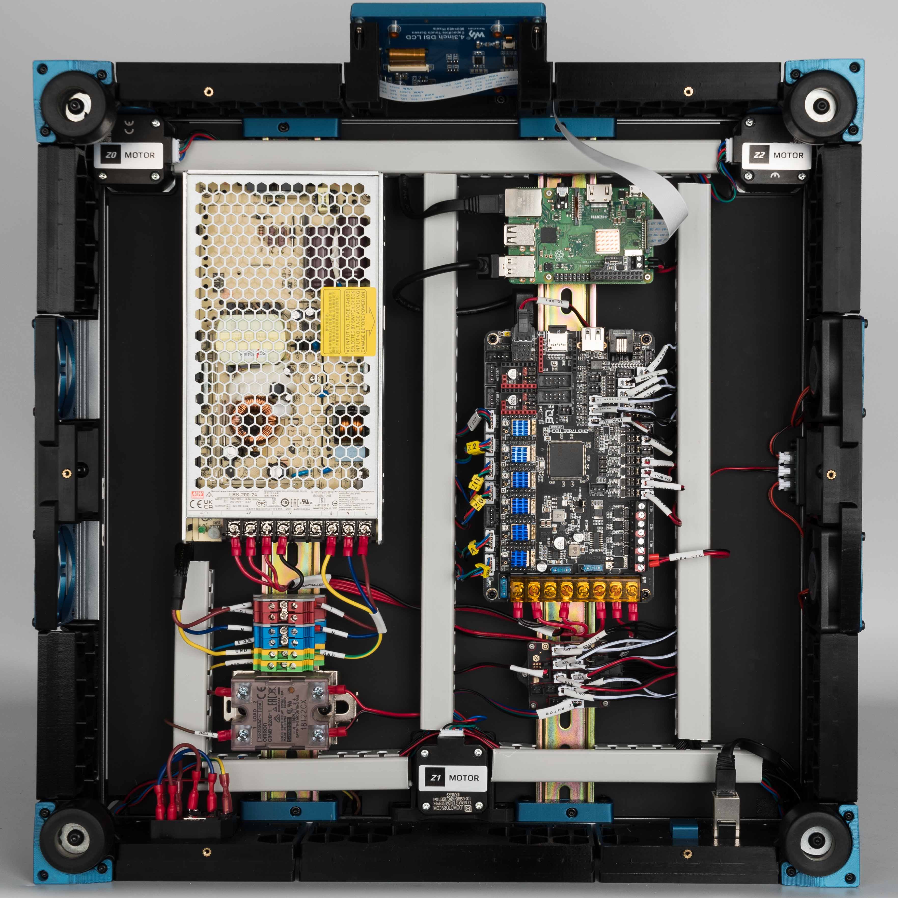
Images/WiringGuide/s15_duct_cover.jpg
