MotorDynamicsLab/LDOVoronTrident/Images/WiringGuide/wago_combo_mount.jpg

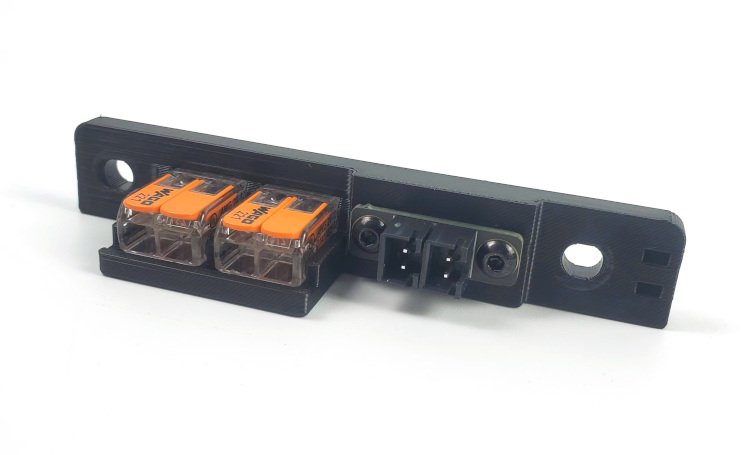
Images/WiringGuide/wago_combo_mount.jpg
